roshbeng/opcua_fusion_test_servers_and_hardware/CAD models/cobot_model/cobot individual components in step format/GRIPPER SUPPORTS I, II & III v5.step

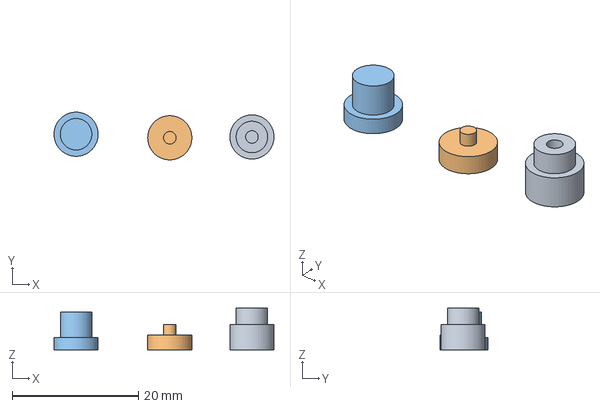
[picture p19: CAD file, 2025-06-16]
CAD models/cobot_model/cobot individual components in step format/GRIPPER SUPPORTS I, II & III v5.step
34.8 x 7.56 x 6.64 mm
