roshbeng/opcua_fusion_test_servers_and_hardware/CAD models/cobot_model/cobot individual components in step format/COBOT'S FOOT.step

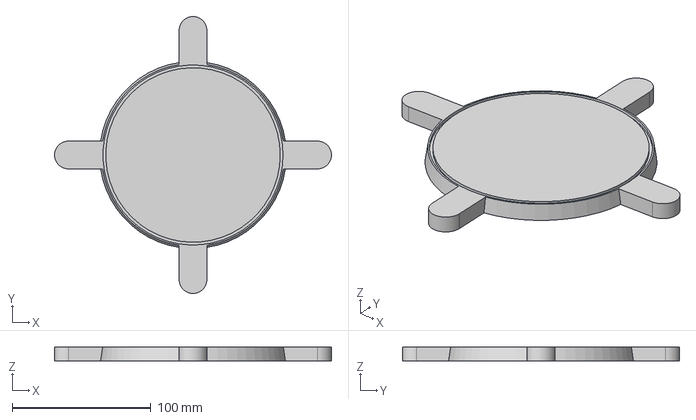
[picture p20: CAD file, 2025-06-16]
CAD models/cobot_model/cobot individual components in step format/COBOT'S FOOT.step
200.0 x 200.0 x 10.0 mm
